cookiemonsternz/Eurorack-VCO/hardware/ltspice/vco.asc

C1: cap; 10n
C2: cap; 100n
C4: cap; 100n
C5: cap; 10n
D1: diode; 1N4148
D2: diode; 1N4148
D3: diode; 1N4148
D4: diode; 1N4148
D5: diode; 1N4148
D6: diode; 1N4148
D7: diode; 1N4148
D8: diode; 1N4148
D9: diode; 1N4148
D10: diode; 1N4148
D11: diode; 1N4148
D12: diode; 1N4148
D13: diode; 1N4148
D14: diode; 1N4148
D15: diode; 1N4148
Q1: pnp; BC557B
Q2: npn; BC547B
R1: res; 10k
R2: res; 10k
R3: res; 1k
R4: res; 1k
R5: res; 100k
R6: res; 10k
R7: res; 1Meg
R8: res; 10k
R9: res; 100k
R10: res; 1Meg
R11: res; 100k
R12: res; 10k
R13: res; 10k
R14: res; 47k
R15: res; 47k
R16: res; 100k
R17: res; 10k
R18: res; 10k
R19: res; 10k
R20: res; 100k
R21: res; 20k
R22: res; 200
R23: res; 2k
R24: res; 100
R25: res; 100
R26: res; 1k
R27: res; 33
R28: res; 33
R29: res; 470
R30: res; 82
R31: res; 82
R32: res; 330
R33: res; 47
R34: res; 47
R35: res; 120
R36: res; 30
R37: res; 30
R38: res; 100k
R39: res; 39
R40: res; 39
R41: res; 100k
R42: res; 1k
R43: res; 1k
R44: res; 1k
R45: res; 10k
R46: res; 10k
R47: res; 1Meg
R48: res; 100k
R49: res; 100k
R50: res; 70k
R51: res; 30k
R52: res; 10k
R53: res; 60k
R54: res; 40k
R55: res; 100k
R56: res; 100k
R57: res; 10k
R58: res; 10k
R59: res; 68k
R60: res; 10k
R61: res; 10k
R62: res; 80k
R63: res; 20k
R64: res; 100k
R65: res; 14k
R66: res; 6.8k
R67: res; 10k
R68: res; 1k
U1: opamp2; TL072
U2: opamp2; TL072
U3: opamp2; TL072
U4: opamp2; TL072
U5: opamp2; TL072
U6: opamp2; TL072
U7: opamp2; TL072
U8: opamp2; TL072
U9: opamp2; TL072
U10: opamp2; TL072
U11: opamp2; TL072
U12: opamp2; TL072
V1: voltage; 24; Rser=1 Cpar=1n
V2: voltage; 0
V3: voltage; 0
V5: voltage; 2.4
V6: voltage; 2.4
Named nets: +Vs, -Vs, 0, CV, SAW, TRI, SIN, FM, PWM, PWM_CV
.SUBCKT TL072    1 2 3 4 5
*
  C1   11 12 3.498E-12
  C2    6  7 15.00E-12
  DC    5 53 DX
  DE   54  5 DX
  DLP  90 91 DX
  DLN  92 90 DX
  DP    4  3 DX
  EGND 99  0 POLY(2) (3,0) (4,0) 0 .5 .5
  FB    7 99 POLY(5) VB VC VE VLP VLN 0 4.715E6 -5E6 5E6 5E6 -5E6
  GA    6  0 11 12 282.8E-6
  GCM   0  6 10 99 8.942E-9
  ISS   3 10 DC 195.0E-6
  HLIM 90  0 VLIM 1K
  J1   11  2 10 JX
  J2   12  1 10 JX
  R2    6  9 100.0E3
  RD1   4 11 3.536E3
  RD2   4 12 3.536E3
  RO1   8  5 150
  RO2   7 99 150
  RP    3  4 2.143E3
  RSS  10 99 1.026E6
  VB    9  0 DC 0
  VC    3 53 DC 2.200
  VE   54  4 DC 2.200
  VLIM  7  8 DC 0
  VLP  91  0 DC 25
  VLN   0 92 DC 25
.MODEL DX D(IS=800.0E-18)
.MODEL JX PJF(IS=15.00E-12 BETA=270.1E-6 VTO=-1)
.ENDS
.tran 0 0.058 0.02
.ac oct 100 20 20000
.dc oct V2 0 10 100
Schmitt Trigger
Buffer, Decouple, Scale
Temp Ind.
INVERTER / SUMMER
TRIM-POT
THERMISTOR
THERMISTOR
TRIM-POT
THERMISTOR
THERMISTOR
PWM
+500R Trimpot
250k POT
100k TRIMPOT
SINE CLIPPER
